JJ-zero/OpenTimingProject/software/OTP-universal-station/pixels.ino

#include <Adafruit_NeoPixel.h>

Adafruit_NeoPixel pixels(18, D4, NEO_GRB + NEO_KHZ800);

bool showingDisconnected = false;
int last_frame = 0;
int last_frame_state = 0;
int active_animation = 0;
/*
  0 - None
  1 - Disconnected
  2 - Run
  3 - Stop
  4 - Signal Base
  5 - Signal Satelite
*/


const uint32_t colorBlack        = pixels.Color(0,     0,   0);
const uint32_t colorStartup      = pixels.Color(100,   0, 200);
const uint32_t colorBase         = pixels.Color(200, 200, 200);
const uint32_t colorSatelite     = pixels.Color(250, 100, 250);
const uint32_t colorDisconnected = pixels.Color(130, 112,   5);
const uint32_t colorLoad         = pixels.Color(255,   0, 255);
const uint32_t colorRun          = pixels.Color(200,   0,   0);
const uint32_t colorStop         = pixels.Color( 15, 250,   0);


void init_pixels() {
  pixels.begin();
  pixels.setBrightness(20);
  pixels.fill(colorBlack);
  pixels.show();
}

void pixelsSetDisconnected() {
  if (showingDisconnected) { return; };
  pixels.fill(colorBlack);
  for (int i = 0; i < 6; i++) {
    pixels.setPixelColor((i*3) + (2 * (1 - (i % 2))), colorDisconnected);
  }
  pixels.show();
  showingDisconnected = true;
}


void pixelsBootAnimation() {
  char g[] = {
    0, 5, 6, 11, 12, 17, // Inner ring
    1, 4, 7, 10, 13, 16, // Midle ring
    2, 3, 8,  9, 14, 15  // Outer ring
  };
  pixels.clear();
  for (int i = 0; i < 18; i++) {
    pixels.setPixelColor(g[i], colorStartup);
    pixels.show();
    delay(75);
  }
}

void pixelsUpdateProgress(int progress) { // progress in 255
  pixels.fill(colorBlack);
  char ring[] = {2, 3, 8,  9, 14, 15};
  for (int i = 0; i < 6; i++) {
    int green = (progress * 6) - (i * 255);
    if (green < 0) {
      green = 0;
    }
    if (green > 255) {
      green = 254;
    }
    int red = 255 - green;
    pixels.setPixelColor(ring[i], pixels.Color(red, green, 0));
  }
  Serial.println(" .");
  pixels.show();
}

void pixelsBase() {
  active_animation = 4;
  pixels.fill(colorBase);
  pixels.show();
}

void pixelsSatelite() {
  active_animation = 5;
  pixels.fill(colorSatelite);
  pixels.show();
}

void pixelsRun() {
  active_animation = 2;
  pixels.fill(colorRun);
  pixels.show();
}

void pixelsStop() {
  active_animation = 3;
  pixels.fill(colorStop);
  pixels.show();
}

void pixelsAnimate() {
  switch (active_animation) {
    case 1:
      // Disconnected
      int now = millis();
      if (now > 250 + last_frame) {
        if (last_frame_state == 0) {
          showingDisconnected = false;
          pixels.clear();
          pixels.show();
        } else {
          pixelsSetDisconnected();
        }
        last_frame_state = 1 - last_frame_state;
        last_frame = now;
      }
    break;
  }
}
