JJ-zero/OpenTimingProject/software/OTP-universal-station/settings.h

IPAddress serverIp(192, 168, 255, 1);
IPAddress APmask(255, 255, 255, 0);
const byte DNS_PORT = 53;

const String open_ssid = "OpenTimingProject";
const String private_ssid = "OpenTimingProjectEvent"; // Eventualy load this from EPROM
